Alexsogge/FancyTable/src/modules/LEDFrameOutput.py

import time
import neopixel
import board
import argparse
from .Helpers import Color, Colors
from .OutputDevice import OutputDevice
from typing import List, Dict, Tuple, Union

class LEDFrameOutput(OutputDevice):

    # LED strip configuration:
    LED_PIN = 18  # GPIO pin connected to the pixels (18 uses PWM!).
    # LED_PIN        = 10      # GPIO pin connected to the pixels (10 uses SPI /dev/spidev0.0).
    LED_FREQ_HZ = 800000  # LED signal frequency in hertz (usually 800khz)
    LED_DMA = 10  # DMA channel to use for generating signal (try 10)
    LED_BRIGHTNESS = 255  # Set to 0 for darkest and 255 for brightest
    LED_INVERT = False  # True to invert the signal (when using NPN transistor level shift)
    LED_CHANNEL = 0  # set to '1' for GPIOs 13, 19, 41, 45 or 53

    def __init__(self, width, height):
        super().__init__(width, height)


        # self.strip = Adafruit_NeoPixel(width*height+1, self.LED_PIN, self.LED_FREQ_HZ, self.LED_DMA, self.LED_INVERT,
        #                           self.LED_BRIGHTNESS, self.LED_CHANNEL)
        self.strip = neopixel.NeoPixel(board.D18, width*height+1, auto_write=False)

        # Intialize the library (must be called once before other functions).
        # self.strip.begin()


    def upload(self, frame_matrix: List[List[Color]]):
        max_led = self.width * self.height
        for y, row in enumerate(frame_matrix):
            for x, col in enumerate(row):
                if y % 2 == 1:
                    x = len(row) - 1 - x
                led_num = (self.height - 1 - y) * self.width + x
                R, G, B = max(min(int(col.r), 255), 0), max(min(int(col.g), 255), 0), \
                          max(min(int(col.b), 255), 0)
                self.strip[led_num] = (R, G, B)
                # print(led_num)
                # print("Write on", led_num, pix)
        self.strip.show()

    def inc_dimming(self, val):
        self.dimming += val
        self.dimming = max(min(self.dimming, 1), 0)

    def set_brightness(self, new_brightness: float):
        self.brightness = max(min(new_brightness, 1), 0)
        self.strip.brightness = self.brightness
